Dzalex/NeedleDCF77/sw/STM32CubeIDE_Project/Core/Src/rtc.c

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
/* Includes ------------------------------------------------------------------*/
#include "rtc.h"

/* USER CODE BEGIN 0 */
#include "stm32l0xx_ll_rtc.h"
#include "interface.h"
/* USER CODE END 0 */

RTC_HandleTypeDef hrtc;

/* RTC init function */
void MX_RTC_Init(void)
{

  RTC_TimeTypeDef sTime = {0};
  RTC_DateTypeDef sDate = {0};
  RTC_AlarmTypeDef sAlarm = {0};

  /** Initialize RTC Only
  */
  hrtc.Instance = RTC;
  hrtc.Init.HourFormat = RTC_HOURFORMAT_12;
  hrtc.Init.AsynchPrediv = 127;
  hrtc.Init.SynchPrediv = 255;
  hrtc.Init.OutPut = RTC_OUTPUT_DISABLE;
  hrtc.Init.OutPutRemap = RTC_OUTPUT_REMAP_NONE;
  hrtc.Init.OutPutPolarity = RTC_OUTPUT_POLARITY_HIGH;
  hrtc.Init.OutPutType = RTC_OUTPUT_TYPE_OPENDRAIN;
  if (HAL_RTC_Init(&hrtc) != HAL_OK)
  {
    Error_Handler();
  }

  /** Initialize RTC and set the Time and Date
  */
  sTime.Hours = 1;
  sTime.Minutes = 59;
  sTime.Seconds = 0;
  sTime.TimeFormat = RTC_HOURFORMAT12_AM;
  sTime.DayLightSaving = RTC_DAYLIGHTSAVING_NONE;
  sTime.StoreOperation = RTC_STOREOPERATION_RESET;
  if (HAL_RTC_SetTime(&hrtc, &sTime, RTC_FORMAT_BIN) != HAL_OK)
  {
    Error_Handler();
  }
  sDate.WeekDay = RTC_WEEKDAY_MONDAY;
  sDate.Month = RTC_MONTH_JANUARY;
  sDate.Date = 1;
  sDate.Year = 0;

  if (HAL_RTC_SetDate(&hrtc, &sDate, RTC_FORMAT_BIN) != HAL_OK)
  {
    Error_Handler();
  }

  /** Enable the Alarm A
  */
  sAlarm.AlarmTime.Hours = 2;
  sAlarm.AlarmTime.Minutes = 0;
  sAlarm.AlarmTime.Seconds = 0;
  sAlarm.AlarmTime.SubSeconds = 0;
  sAlarm.AlarmTime.TimeFormat = RTC_HOURFORMAT12_AM;
  sAlarm.AlarmTime.DayLightSaving = RTC_DAYLIGHTSAVING_NONE;
  sAlarm.AlarmTime.StoreOperation = RTC_STOREOPERATION_RESET;
  sAlarm.AlarmMask = RTC_ALARMMASK_DATEWEEKDAY;
  sAlarm.AlarmSubSecondMask = RTC_ALARMSUBSECONDMASK_NONE;
  sAlarm.AlarmDateWeekDaySel = RTC_ALARMDATEWEEKDAYSEL_DATE;
  sAlarm.AlarmDateWeekDay = 1;
  sAlarm.Alarm = RTC_ALARM_A;
  if (HAL_RTC_SetAlarm_IT(&hrtc, &sAlarm, RTC_FORMAT_BIN) != HAL_OK)
  {
    Error_Handler();
  }

  /** Enable the WakeUp
  */
  if (HAL_RTCEx_SetWakeUpTimer_IT(&hrtc, 0, RTC_WAKEUPCLOCK_CK_SPRE_16BITS) != HAL_OK)
  {
    Error_Handler();
  }
  /* USER CODE BEGIN RTC_Init 2 */
  LL_RTC_DisableWriteProtection(hrtc.Instance);
  LL_RTC_CAL_SetMinus(hrtc.Instance, RTC_CAL_CALM_VALUE);
  LL_RTC_EnableWriteProtection(hrtc.Instance);
  /* USER CODE END RTC_Init 2 */

}

void HAL_RTC_MspInit(RTC_HandleTypeDef* rtcHandle)
{

  if(rtcHandle->Instance==RTC)
  {
    /* RTC clock enable */
    __HAL_RCC_RTC_ENABLE();

    /* RTC interrupt Init */
    HAL_NVIC_SetPriority(RTC_IRQn, 3, 0);
    HAL_NVIC_EnableIRQ(RTC_IRQn);
  }
}

void HAL_RTC_MspDeInit(RTC_HandleTypeDef* rtcHandle)
{

  if(rtcHandle->Instance==RTC)
  {
    /* Peripheral clock disable */
    __HAL_RCC_RTC_DISABLE();

    /* RTC interrupt Deinit */
    HAL_NVIC_DisableIRQ(RTC_IRQn);
  }
}

/* USER CODE BEGIN 1 */
void HAL_RTCEx_WakeUpTimerEventCallback(RTC_HandleTypeDef *hrtc)
{
	osEventFlagsSet(interfaceEventHandle, INTERFACE_SECOND_FLAG);
}

void HAL_RTC_AlarmAEventCallback(RTC_HandleTypeDef *hrtc)
{
	osEventFlagsSet(interfaceEventHandle, INTERFACE_2AM_FLAG);
}
/* USER CODE END 1 */
