Dzalex/NeedleDCF77/sw/STM32CubeIDE_Project/Core/Src/vfd.c

/*
 * vfd.c
 *
 *  Created on: Nov 25, 2023
 *      Author: Dzale
 */
#include "spi.h"
#include "tim.h"
#include "cmsis_os.h"

#include "vfd.h"
#include "vfd_font.h"
#include "powerManagement.h"

/* General constants for PT6312 */
const uint8_t PT6312_BYTES_PER_GRID = 2;
const uint8_t PT6312_MEMORY_SIZE = 0x16;
const uint8_t VFD_GRIDS = 9;
const uint8_t VFD_SEGMENTS = 8;
const uint8_t VFD_SELECTED_BRIGHTNESS = 0x03;

/* COMMAND 1: DISPLAY MODE SETTING COMMANDS */
const uint8_t VFD_DISPLAY_MODE_9DIG_13SEG = 0x05;
const uint8_t VFD_DISPLAY_MODE_11DIG_11SEG = 0x07;

/* COMMAND 2: DATA SETTING COMMANDS */
const uint8_t VFD_DATA_SETTING_WRITE_TO_DISPLAY_MODE = 0x40;	/* Increment address after data has been written */

const uint8_t VFD_INCREMENT_ADDRESS = 0x00;
const uint8_t VFD_FIXED_ADDRESS = 0x02;

const uint8_t VFD_TEST_MODE = 0x04;

/* COMMAND 3: ADDRESS SETTING COMMANDS */
const uint8_t VFD_ADDRESS_COMAND_BASE = 0xC0;	/* Address: 0x00 to 15 */

/* COMMAND 4: DISPLAY CONTROL COMMANDS */
const uint8_t VFD_BRIGHTNESS_BASE = 0x88;	/* Brightness 0 to 7 */
const uint8_t VFD_OFF = 0x80;

const uint32_t SPI_TIMEOUT = 100;


/* Forward declaration of local functions */
static void VFD_Command(uint8_t command);
static void VFD_AddressSettingCommand(uint8_t address);
static void VFD_ActivateStrobe();
static void VFD_DeactivateStrobe();


void VFD_PowerOnAndInitialize()
{
	//Turn on 4V
	LTC_Enable4VoltRail();

	//Activate PWM Fosc
	HAL_TIM_PWM_Start(&htim2, TIM_CHANNEL_1);

	//Turn on 24V
	LT1617_EnableNeg24VRail();

	//Delay 200ms
	osDelay(200);

	__HAL_SPI_ENABLE(&hspi1);

	//Set Command 2 to write data
	VFD_Command(VFD_DATA_SETTING_WRITE_TO_DISPLAY_MODE | VFD_INCREMENT_ADDRESS);

	//Set Command 3 to clear Display ram
	VFD_Clear();

	//Set Command 1 Mode 9dig 13seg
	VFD_Command(VFD_DISPLAY_MODE_9DIG_13SEG);

	//Set Command 4 to turn on display with brightness
	VFD_Command(VFD_BRIGHTNESS_BASE | VFD_SELECTED_BRIGHTNESS);
}

void VFD_PowerOffAndDeinitialize()
{
	LT1617_DisableNeg24VRail();
	HAL_TIM_PWM_Stop(&htim2, TIM_CHANNEL_1);
	LTC_Disable4VoltRail();
	__HAL_SPI_DISABLE(&hspi1);
}

void VFD_Command(uint8_t command)
{
	VFD_ActivateStrobe();
	HAL_SPI_Transmit(&hspi1, &command, 1, SPI_TIMEOUT);
	VFD_DeactivateStrobe();
}

void VFD_AddressSettingCommand(uint8_t address)
{
	VFD_ActivateStrobe();
	uint8_t addressSettingCommand = VFD_ADDRESS_COMAND_BASE + address;
	HAL_SPI_Transmit(&hspi1, &addressSettingCommand, 1, SPI_TIMEOUT);
}

void VFD_Clear()
{
	VFD_AddressSettingCommand(0);
	uint8_t no_data = 0x00;

	for(uint8_t i = 0; i < PT6312_MEMORY_SIZE; i++)
	{
		HAL_SPI_Transmit(&hspi1, &no_data, 1, SPI_TIMEOUT);
	}

	VFD_DeactivateStrobe();
}

void VFD_PrintDigitAtPosition(uint8_t digit, uint8_t possition)
{
	if(possition >= VFD_GRIDS)
		return;

	if(digit > 9)
		return;

	VFD_WriteDataToDsiplayAtPosition((uint8_t *)&VFD_FONT_NUMBERS[digit], 1, possition);
}

void VFD_PrintCharacterAtPosition(char digit, uint8_t position)
{
	if(position >= VFD_GRIDS)
		return;

	if(digit < 'a' || digit > 'z')
		return;

	uint8_t characterToWrite = digit - 'a';

	VFD_WriteDataToDsiplayAtPosition((uint8_t *)&VFD_FONT_LETTERS[characterToWrite], 1, position);
}

void VFD_PrintPositiveNumber(uint32_t number)
{
	uint8_t numberDataBuffer[9] = {0, 0, 0, 0, 0, 0, 0, 0, VFD_FONT_NUMBERS[0]};
	int8_t i = 8;

	if(number > 999999999)
	{
		return;
	}

	while(i >= 0 && number != 0)
	{
		numberDataBuffer[i] = VFD_FONT_NUMBERS[number % 10];
		number = number / 10;
		i--;
	}

	VFD_WriteDataToDsiplayAtPosition(numberDataBuffer, sizeof(numberDataBuffer), 0);
}

void VFD_WriteDataToDsiplayAtPosition(uint8_t *data, uint8_t size, uint8_t position)
{
	if(position >= VFD_GRIDS){
		return;
	}

	uint8_t addressForPossition = position * PT6312_BYTES_PER_GRID;
	uint8_t allOff = 0x00;

	VFD_Command(VFD_DATA_SETTING_WRITE_TO_DISPLAY_MODE);
	VFD_AddressSettingCommand(addressForPossition);

	for(uint8_t i = 0; i < size; i++)
	{
		HAL_SPI_Transmit(&hspi1, ( (uint8_t *)data + i ), 1, SPI_TIMEOUT);
		HAL_SPI_Transmit(&hspi1, &allOff, 1, SPI_TIMEOUT);
	}

	VFD_DeactivateStrobe();

	VFD_Command(VFD_DISPLAY_MODE_9DIG_13SEG);
	VFD_Command(VFD_BRIGHTNESS_BASE | VFD_SELECTED_BRIGHTNESS);
}

void VFD_ActivateStrobe()
{
	HAL_GPIO_WritePin(VFD_STB_GPIO_Port, VFD_STB_Pin, GPIO_PIN_RESET);
}

void VFD_DeactivateStrobe()
{
	HAL_GPIO_WritePin(VFD_STB_GPIO_Port, VFD_STB_Pin, GPIO_PIN_SET);
}

void VFD_Test()
{
	for(int i = 0; i < 26; i++)
	{
		VFD_PrintCharacterAtPosition('a' + i, i % 9);
		osDelay(200);
	}

	VFD_Clear();
	VFD_PrintCharacterAtPosition('t', 0);
	VFD_PrintCharacterAtPosition('e', 1);
	VFD_PrintCharacterAtPosition('s', 2);
	VFD_PrintCharacterAtPosition('t', 3);

	osDelay(1000);
	VFD_Clear();
}
