Dzalex/NeedleDCF77/sw/STM32CubeIDE_Project/Core/Inc/vfd_font.h

/*
 * vfd_font.h
 *
 *  Created on: Nov 28, 2023
 *      Author: Dzale
 */

#ifndef INC_VFD_FONT_H_
#define INC_VFD_FONT_H_

extern const uint8_t VFD_FONT_NUMBERS[];
extern const uint8_t VFD_FONT_LETTERS[];

extern const uint8_t VFD_ACTIVATE_DOT;	/* Do an OR operation with character that you want to show DOT with	*/

#endif /* INC_VFD_FONT_H_ */
